LjungrennAudio/ryomodular.com_vert_mx/docs/vertmix/downloads/vertmix pcb 1 schematic.png

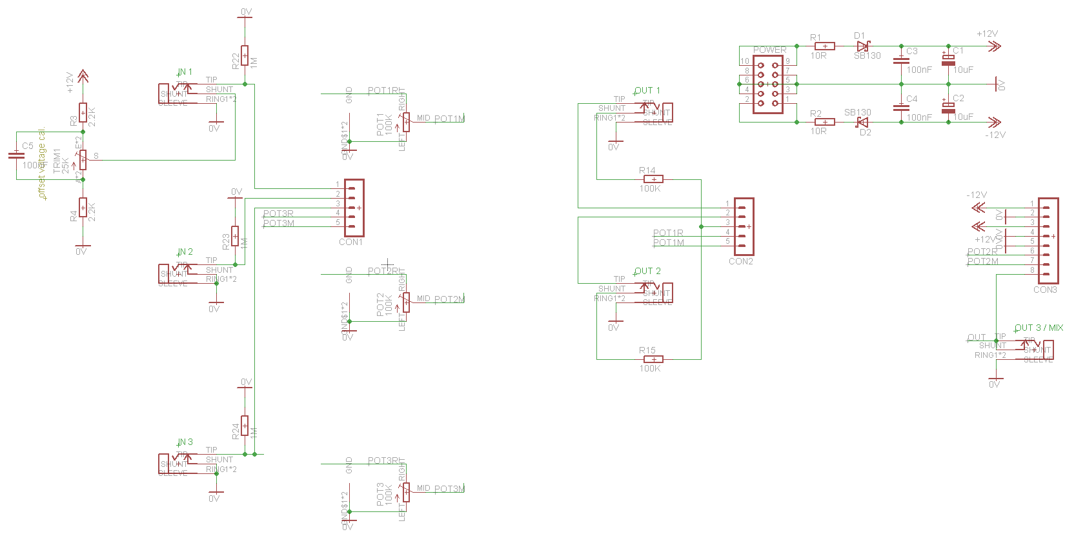
docs/vertmix/downloads/vertmix pcb 1 schematic.png
