LjungrennAudio/ryomodular.com_vert_mx/src/vert_mx - Copy.png

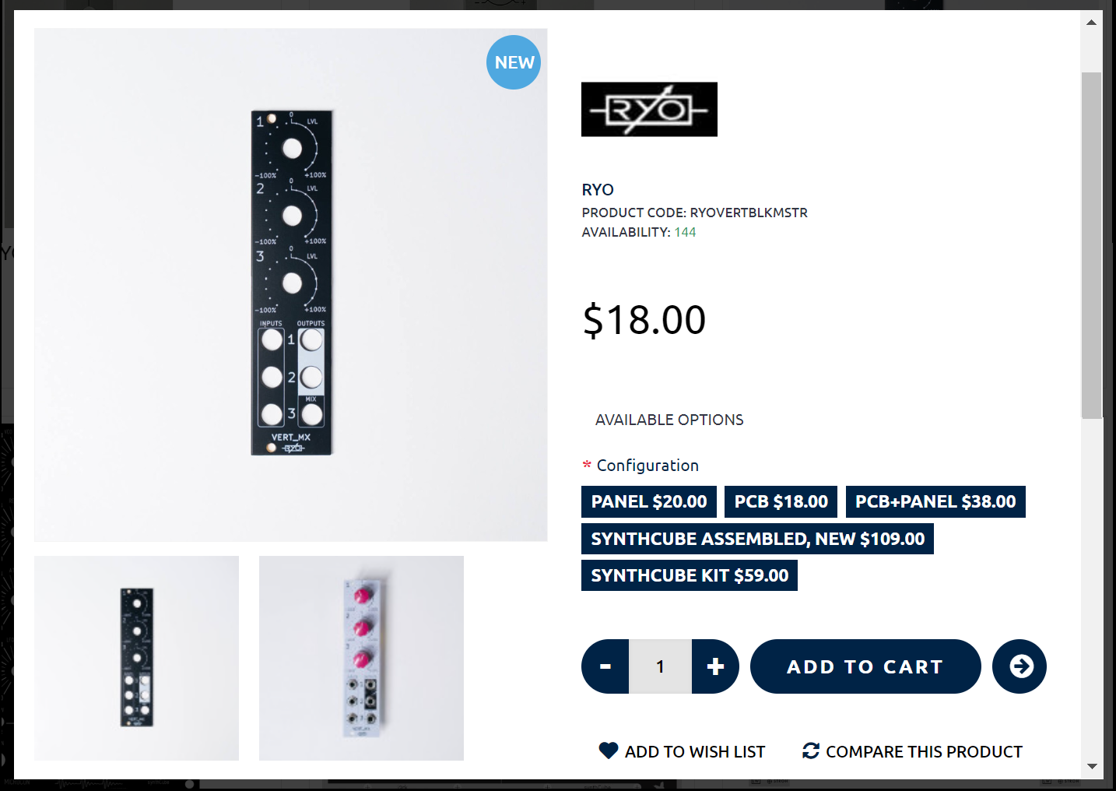
src/vert_mx - Copy.png
