LjungrennAudio/ryomodular.com_vert_mx/src/vert_mx/ryomodular-vert_mx-schem-202411160015.png

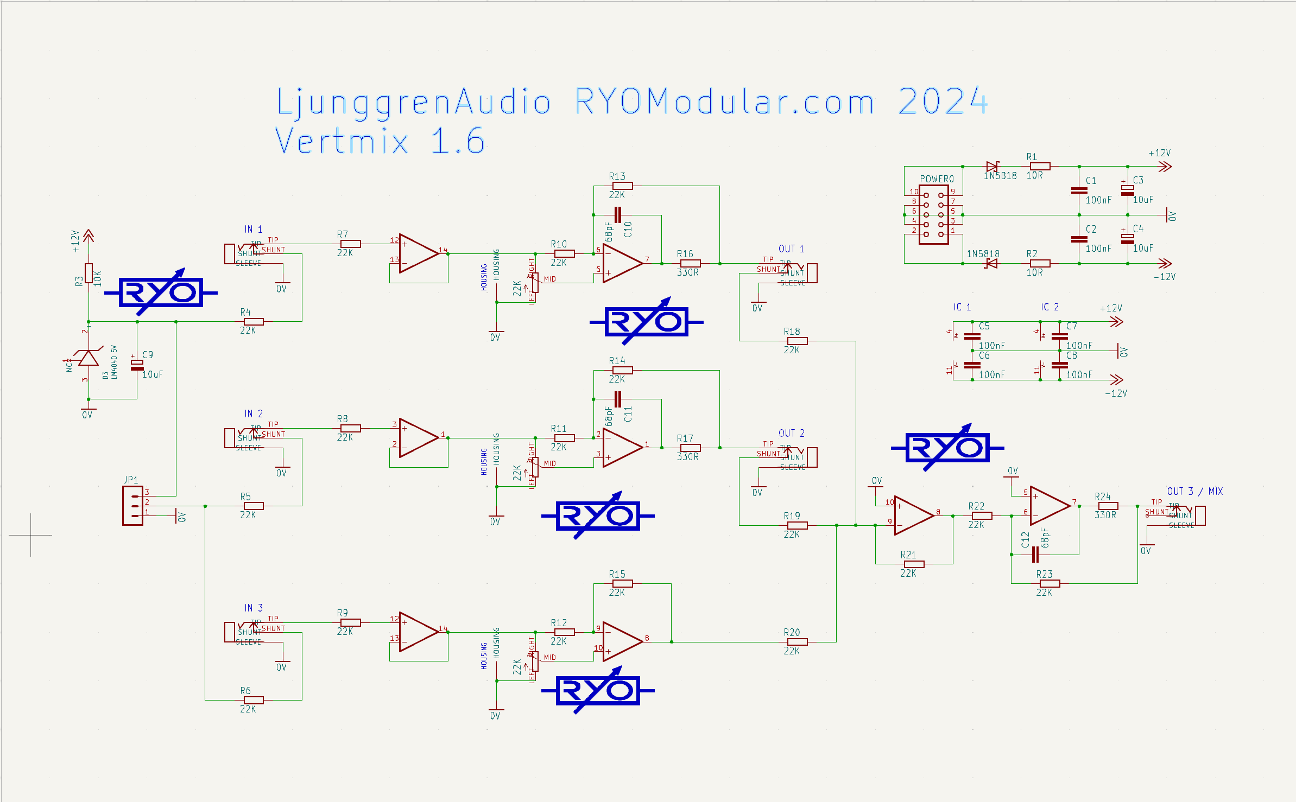
src/vert_mx/ryomodular-vert_mx-schem-202411160015.png
