LjungrennAudio/ryomodular.com_vert_mx/src/vert_mx_schematic_2410021019 - Copy.gif

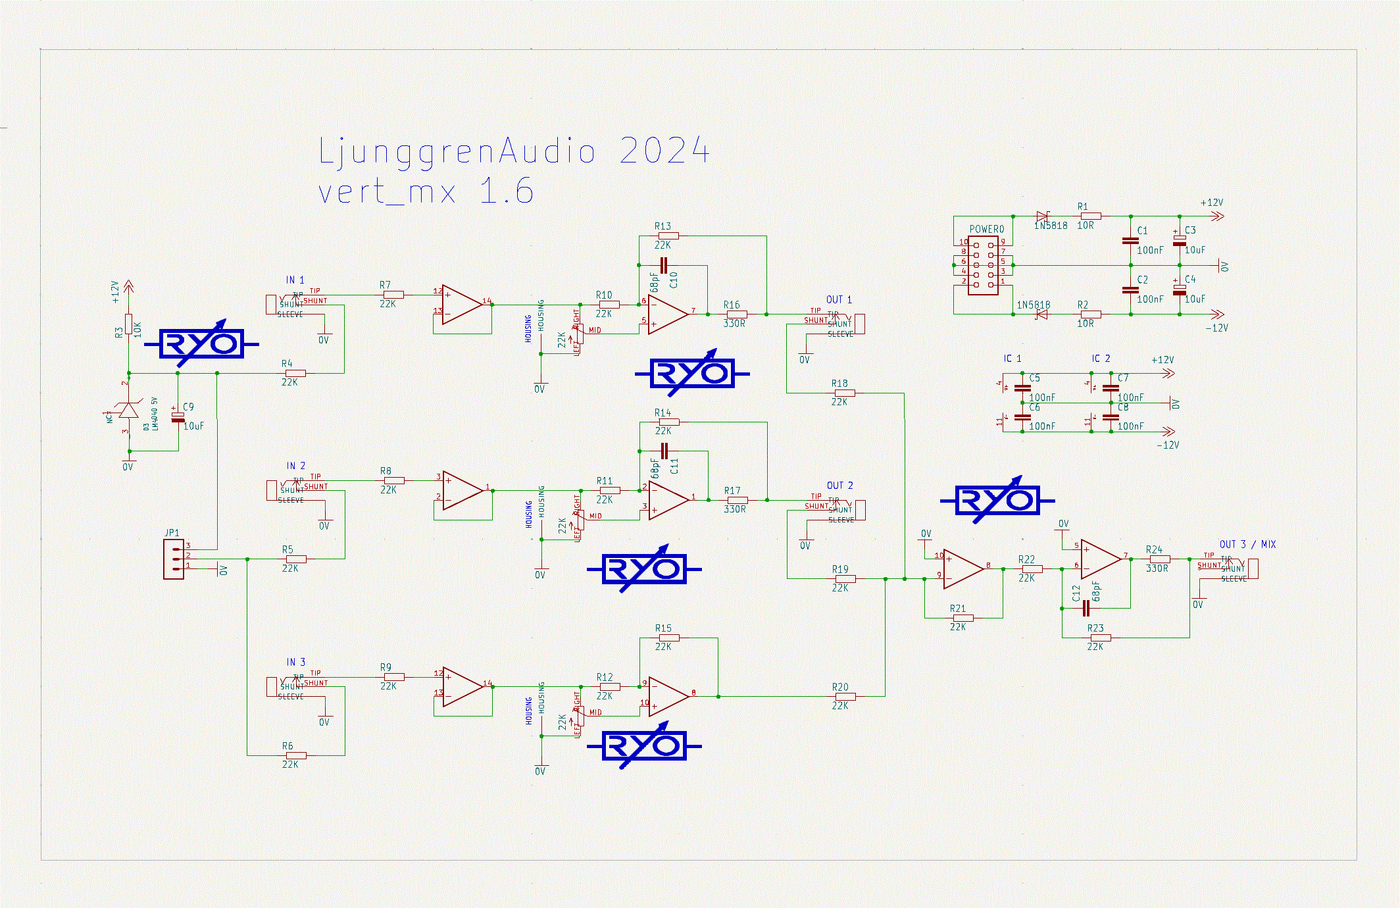
src/vert_mx_schematic_2410021019 - Copy.gif
