LjungrennAudio/ryomodular.com_vert_mx/src/vertmix_docs_etc-/Bipolar mixer-att 1.0.png

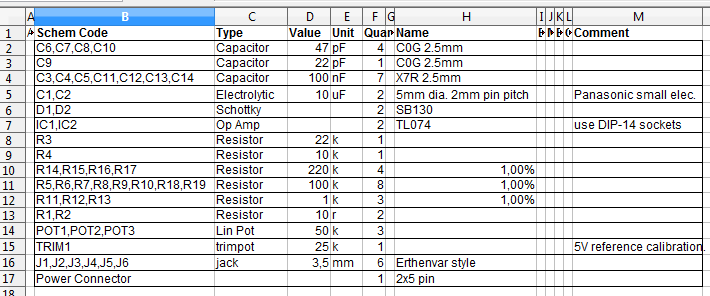
src/vertmix_docs_etc-/Bipolar mixer-att 1.0.png
