LjungrennAudio/ryomodular.com_vert_mx/builds/ryo_vert_mx/3ch mix.brd

## EAGLE design builds/ryo_vert_mx/3ch mix.brd (2024-09-06)

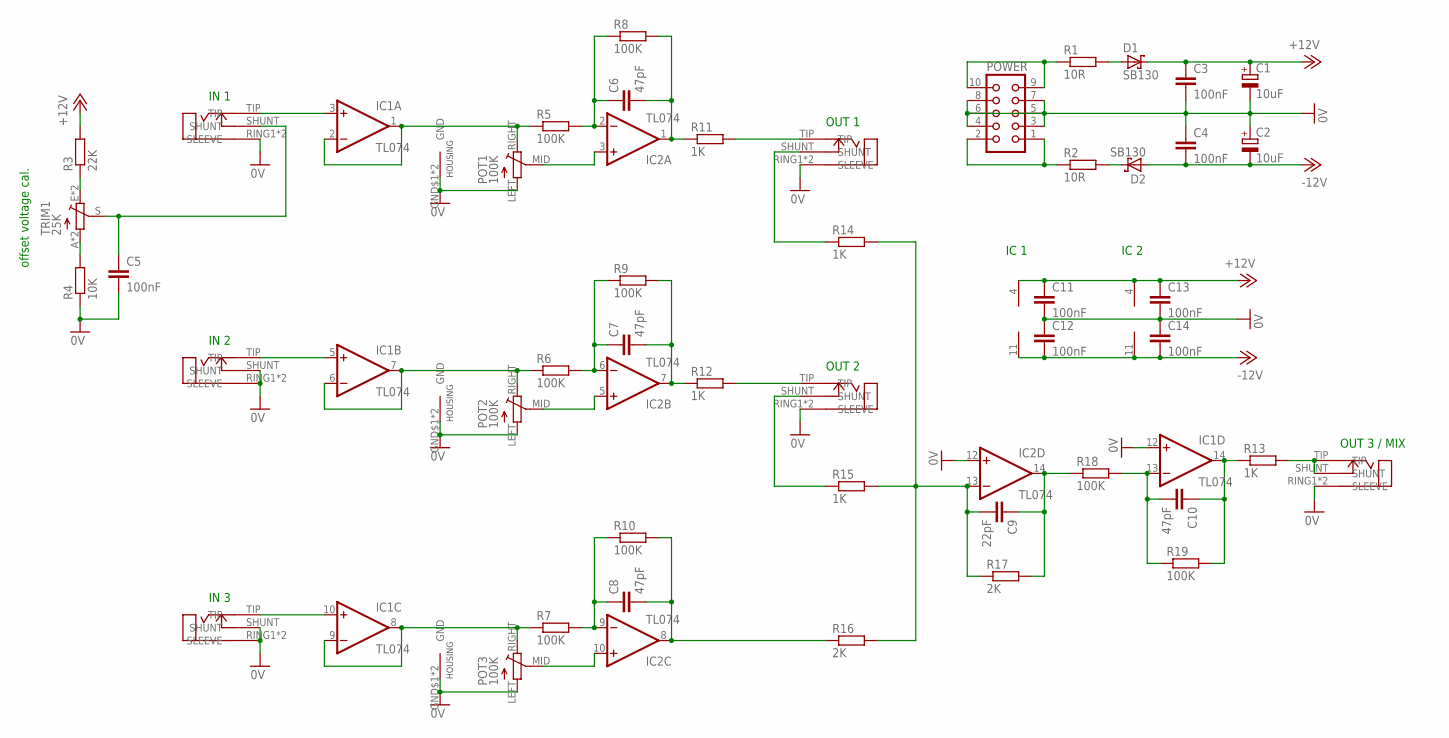
[picture p53: schematic 3ch mix.sch]

Parts:
C1, C2: 10uF; E2-5
C3, C4, C5, C11, C12, C13, C14: 100nF; C025-024X044
C6, C7, C8, C10: 47pF; C025-024X044
C9: 22pF; C025-024X044
D1, D2: SB130; DO41-7
IC1, IC2: TL074; DIL14
IN1, IN2, IN3: ERTHENVAR_3.5MM_JACK; ERTHENVAR
OUT1, OUT2, OUT3: ERTHENVAR_3.5MM_JACK; ERTHENVAR
POT1, POT2, POT3: 100K; POT-ALPHA9
POWER: CON10L
R1, R2: 10R; 0207/9
R3: 22K; 0207/9
R4: 10K; 0207/9
R5, R6, R7, R8, R9, R10, R18, R19: 100K; 0207/9
R11, R12, R13, R14, R15: 1K; 0207/9
R16, R17: 2K; 0207/9
TRIM1: 25K; B25P

Connections:
0V: C1.-, C2.+, C3.2, C4.1, C5.2, C11.2, C12.1, C13.2, C14.1, IC1.12 (+IN), IC2.12 (+IN), IN1.RING1 (SLEEVE), IN1.RING2 (SLEEVE), IN2.RING1 (SLEEVE), IN2.RING2 (SLEEVE), IN2.SHUNT, IN3.RING1 (SLEEVE), IN3.RING2 (SLEEVE), IN3.SHUNT, OUT1.RING1 (SLEEVE), OUT1.RING2 (SLEEVE), OUT2.RING1 (SLEEVE), OUT2.RING2 (SLEEVE), OUT3.RING1 (SLEEVE), OUT3.RING2 (SLEEVE), POT1.GND$1 (GND), POT1.GND$2 (GND), POT1.LEFT, POT2.GND$1 (GND), POT2.GND$2 (GND), POT2.LEFT, POT3.GND$1 (GND), POT3.GND$2 (GND), POT3.LEFT, POWER.3, POWER.4, POWER.5, POWER.6, POWER.7, POWER.8, R4.1
+12V: C1.+, C3.1, C11.1, C13.1, D1.C, IC1.4 (V+), IC2.4 (V+), R3.2
-12V: C2.-, C4.2, C12.2, C14.2, D2.A, IC1.11 (V-), IC2.11 (V-)
unnamed: POWER.9, POWER.10, R1.1
unnamed: POWER.1, POWER.2, R2.1
unnamed: R4.2, TRIM1.A, TRIM1.AA (A)
unnamed: D1.A, R1.2
unnamed: D2.C, R2.2
unnamed: R3.1, TRIM1.E, TRIM1.EE (E)
unnamed: C5.1, IN1.SHUNT, TRIM1.S
unnamed: IC1.3 (+IN), IN1.TIP
unnamed: IC1.5 (+IN), IN2.TIP
unnamed: IC1.10 (+IN), IN3.TIP
unnamed: IC1.1 (OUT), IC1.2 (-IN), POT1.RIGHT, R5.1
unnamed: IC1.6 (-IN), IC1.7 (OUT), POT2.RIGHT, R6.1
unnamed: IC1.8 (OUT), IC1.9 (-IN), POT3.RIGHT, R7.1
unnamed: C6.1, IC2.2 (-IN), R5.2, R8.1
unnamed: IC2.3 (+IN), POT1.MID
unnamed: IC2.5 (+IN), POT2.MID
unnamed: IC2.10 (+IN), POT3.MID
unnamed: OUT1.TIP, R11.2
unnamed: OUT2.TIP, R12.2
unnamed: C7.1, IC2.6 (-IN), R6.2, R9.1
unnamed: C8.1, IC2.9 (-IN), R7.2, R10.1
unnamed: C6.2, IC2.1 (OUT), R8.2, R11.1
unnamed: C7.2, IC2.7 (OUT), R9.2, R12.1
unnamed: C8.2, IC2.8 (OUT), R10.2, R16.1
unnamed: OUT1.SHUNT, R14.1
unnamed: OUT2.SHUNT, R15.1
unnamed: C9.2, IC2.13 (-IN), R14.2, R15.2, R16.2, R17.1
unnamed: C9.1, IC2.14 (OUT), R17.2, R18.1
unnamed: C10.2, IC1.13 (-IN), R18.2, R19.1
unnamed: C10.1, IC1.14 (OUT), R13.1, R19.2
unnamed: OUT3.SHUNT, OUT3.TIP, R13.2

Notes on the sheet:
offset voltage cal.
IN 1
IN 2
IN 3
OUT 1
OUT 2
OUT 3 / MIX
IC 1
IC 2
HOUSING

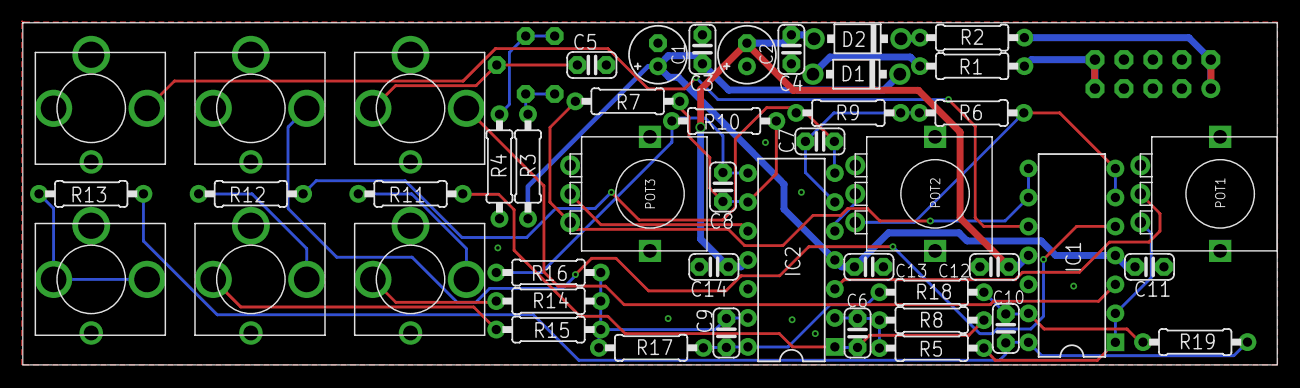
[picture p54: board 3ch mix.brd from above]

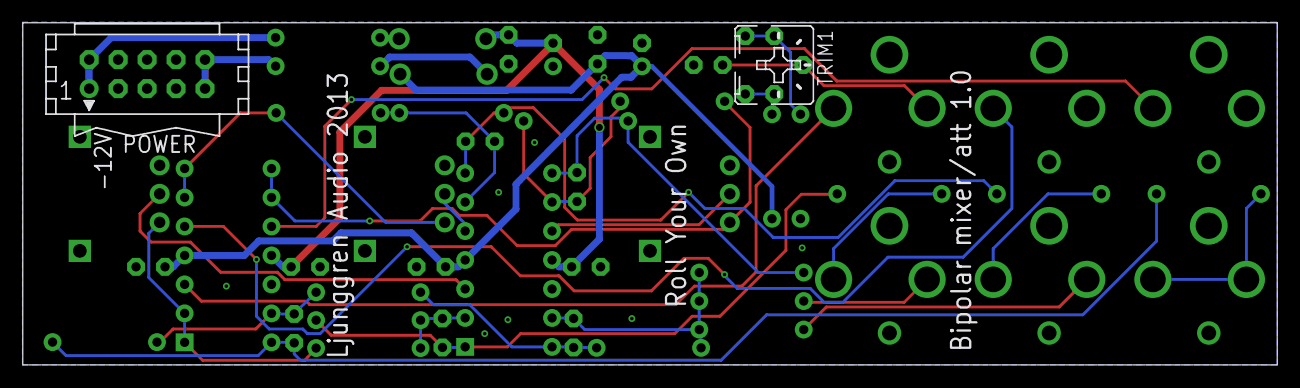
[picture p55: board 3ch mix.brd from below]

Board: 2 copper layers, 110.0 x 30.0 mm, 48 parts (2 on the bottom side), 34 nets.
