LjungrennAudio/ryomodular.com_vert_mx/builds/ryo_vert_mx/PCB1 1.1.brd

## EAGLE design builds/ryo_vert_mx/PCB1 1.1.brd (2024-09-06)

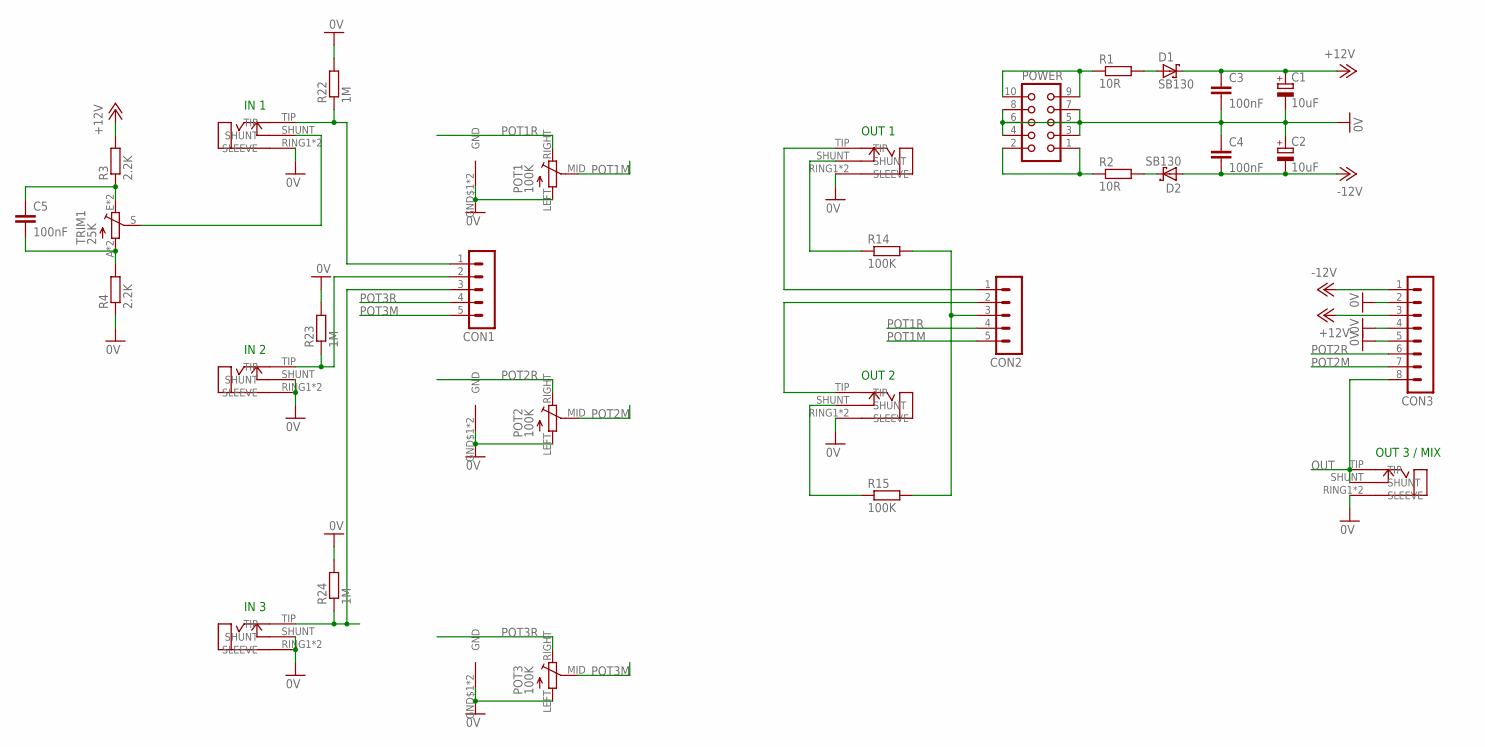
[picture p56: schematic PCB1 1.1.sch]

Parts:
C1, C2: 10uF; E2-5
C3, C4, C5: 100nF; C025-024X044
CON1, CON2: MA05-1
CON3: MA08-1
D1, D2: SB130; DO41-7
IN1, IN2, IN3: ERTHENVAR_3.5MM_JACK; ERTHENVAR
OUT1, OUT2, OUT3: ERTHENVAR_3.5MM_JACK; ERTHENVAR
POT1, POT2, POT3: 100K; POT-ALPHA9
POWER: CON10L
R1, R2: 10R; 0207/9
R3, R4: 2.2K; 0207/9
R14, R15: 100K; 0207/9
R22, R23, R24: 1M; 0207/9
TRIM1: 25K; B25P

Connections:
0V: C1.-, C2.+, C3.2, C4.1, CON3.2, CON3.4, CON3.5, IN1.RING1 (SLEEVE), IN1.RING2 (SLEEVE), IN2.RING1 (SLEEVE), IN2.RING2 (SLEEVE), IN2.SHUNT, IN3.RING1 (SLEEVE), IN3.RING2 (SLEEVE), IN3.SHUNT, OUT1.RING1 (SLEEVE), OUT1.RING2 (SLEEVE), OUT2.RING1 (SLEEVE), OUT2.RING2 (SLEEVE), OUT3.RING1 (SLEEVE), OUT3.RING2 (SLEEVE), POT1.GND$1 (GND), POT1.GND$2 (GND), POT1.LEFT, POT2.GND$1 (GND), POT2.GND$2 (GND), POT2.LEFT, POT3.GND$1 (GND), POT3.GND$2 (GND), POT3.LEFT, POWER.3, POWER.4, POWER.5, POWER.6, POWER.7, POWER.8, R4.1, R22.2, R23.2, R24.2
+12V: C1.+, C3.1, CON3.3, D1.C, R3.2
-12V: C2.-, C4.2, CON3.1, D2.A
unnamed: POWER.9, POWER.10, R1.1
unnamed: POWER.1, POWER.2, R2.1
unnamed: C5.2, R4.2, TRIM1.A, TRIM1.AA (A)
unnamed: D1.A, R1.2
unnamed: D2.C, R2.2
unnamed: C5.1, R3.1, TRIM1.E, TRIM1.EE (E)
unnamed: IN1.SHUNT, TRIM1.S
unnamed: CON1.1, IN1.TIP, R22.1
unnamed: CON1.2, IN2.TIP, R23.1
unnamed: CON1.3, IN3.TIP, R24.1
unnamed: CON2.1, OUT1.TIP
unnamed: CON2.2, OUT2.TIP
unnamed: OUT1.SHUNT, R14.1
unnamed: OUT2.SHUNT, R15.1
unnamed: CON2.3, R14.2, R15.2
OUT: CON3.8, OUT3.SHUNT, OUT3.TIP
POT1M: CON2.5, POT1.MID
POT1R: CON2.4, POT1.RIGHT
POT2M: CON3.7, POT2.MID
POT2R: CON3.6, POT2.RIGHT
POT3M: CON1.5, POT3.MID
POT3R: CON1.4, POT3.RIGHT

Notes on the sheet:
IN 1
IN 2
IN 3
OUT 1
OUT 2
OUT 3 / MIX

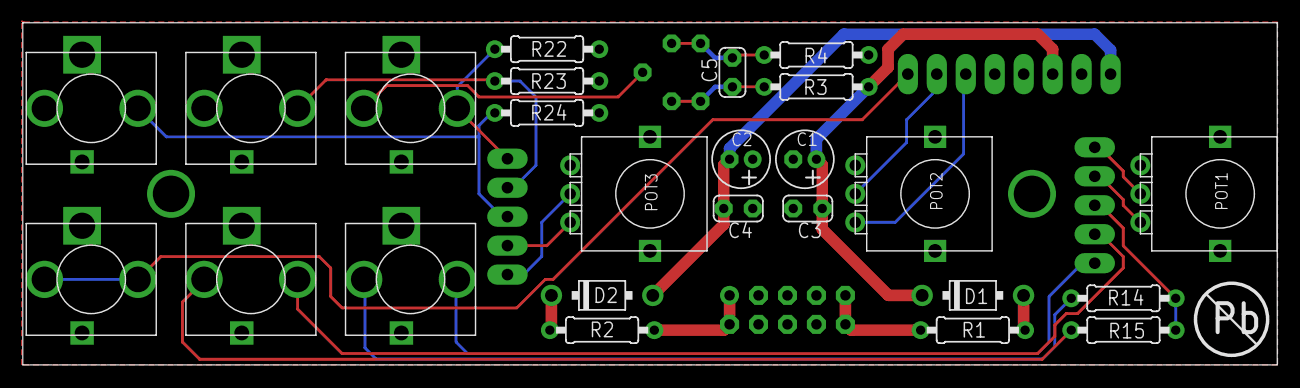
[picture p57: board PCB1 1.1.brd from above]

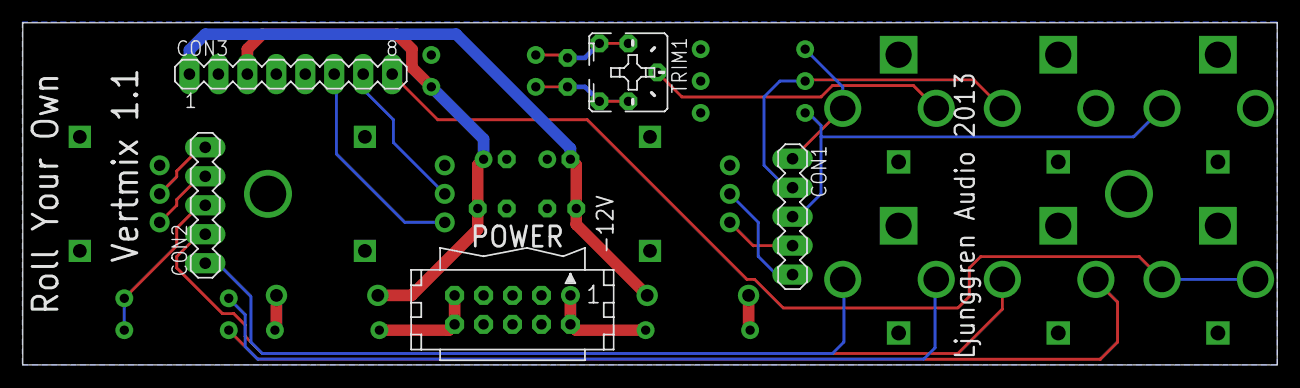
[picture p58: board PCB1 1.1.brd from below]

Board: 2 copper layers, 110.0 x 30.0 mm, 30 parts (5 on the bottom side), 25 nets.
