LjungrennAudio/ryomodular.com_vert_mx/builds/ryo_vert_mx/PCB2 1.1.brd

## EAGLE design builds/ryo_vert_mx/PCB2 1.1.brd (2024-09-06)

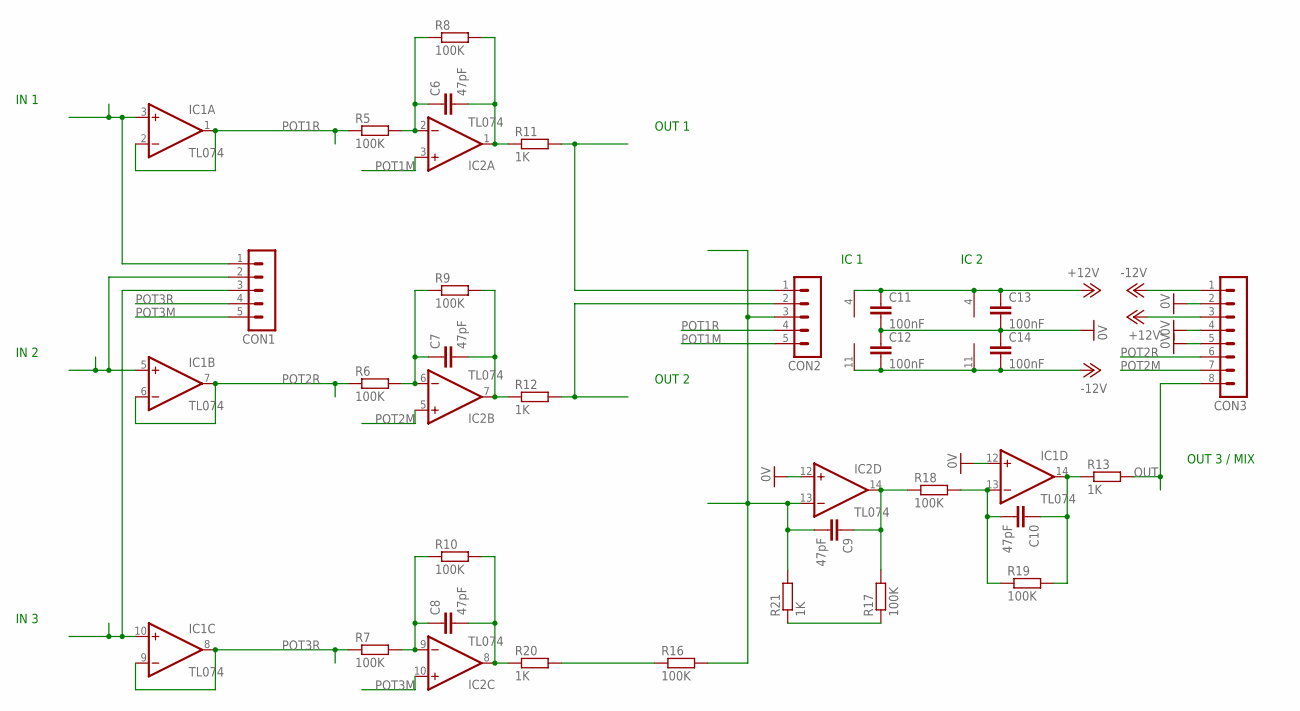
[picture p59: schematic PCB2 1.1.sch]

Parts:
C6, C7, C8, C9, C10: 47pF; C025-024X044
C11, C12, C13, C14: 100nF; C025-024X044
CON1, CON2: MA05-1
CON3: MA08-1
IC1, IC2: TL074; DIL14
R5, R6, R7, R8, R9, R10, R16, R17, R18, R19: 100K; 0207/9
R11, R12, R13, R20, R21: 1K; 0207/9

Connections:
0V: C11.2, C12.1, C13.2, C14.1, CON3.2, CON3.4, CON3.5, IC1.12 (+IN), IC2.12 (+IN)
+12V: C11.1, C13.1, CON3.3, IC1.4 (V+), IC2.4 (V+)
-12V: C12.2, C14.2, CON3.1, IC1.11 (V-), IC2.11 (V-)
unnamed: R16.1, R20.2
unnamed: CON1.1, IC1.3 (+IN)
unnamed: CON1.2, IC1.5 (+IN)
unnamed: CON1.3, IC1.10 (+IN)
unnamed: C6.1, IC2.2 (-IN), R5.2, R8.1
unnamed: CON2.1, R11.2
unnamed: CON2.2, R12.2
unnamed: C7.1, IC2.6 (-IN), R6.2, R9.1
unnamed: C8.1, IC2.9 (-IN), R7.2, R10.1
unnamed: C6.2, IC2.1 (OUT), R8.2, R11.1
unnamed: C7.2, IC2.7 (OUT), R9.2, R12.1
unnamed: C8.2, IC2.8 (OUT), R10.2, R20.1
unnamed: R17.1, R21.1
unnamed: C9.1, IC2.14 (OUT), R17.2, R18.1
unnamed: C10.2, IC1.13 (-IN), R18.2, R19.1
unnamed: C10.1, IC1.14 (OUT), R13.1, R19.2
unnamed: C9.2, CON2.3, IC2.13 (-IN), R16.2, R21.2
OUT: CON3.8, R13.2
POT1M: CON2.5, IC2.3 (+IN)
POT1R: CON2.4, IC1.1 (OUT), IC1.2 (-IN), R5.1
POT2M: CON3.7, IC2.5 (+IN)
POT2R: CON3.6, IC1.6 (-IN), IC1.7 (OUT), R6.1
POT3M: CON1.5, IC2.10 (+IN)
POT3R: CON1.4, IC1.8 (OUT), IC1.9 (-IN), R7.1

Notes on the sheet:
IN 1
IN 2
IN 3
OUT 1
OUT 2
OUT 3 / MIX
IC 1
IC 2

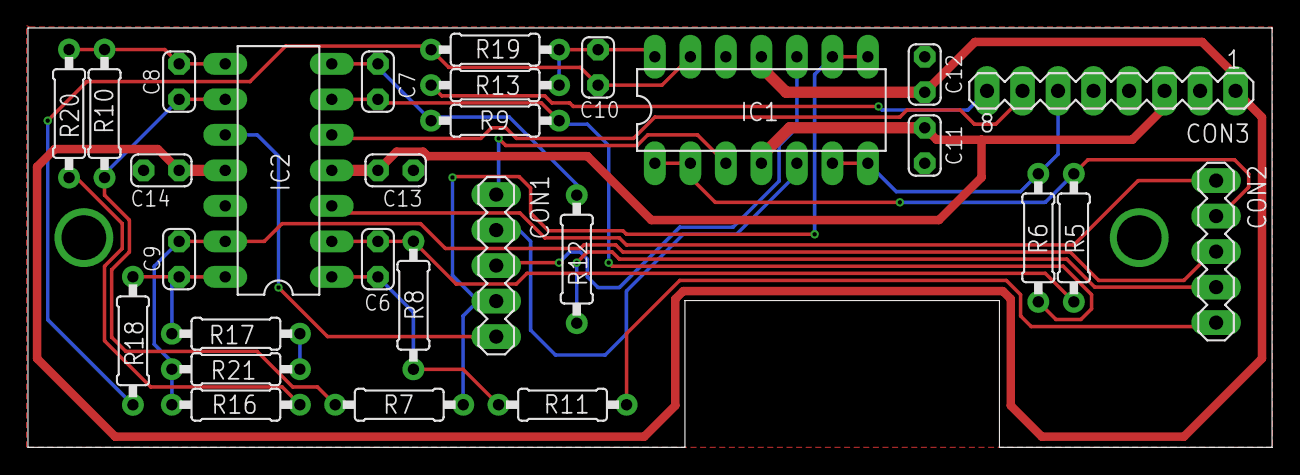
[picture p60: board PCB2 1.1.brd from above]

Board: 2 copper layers, 89.0 x 30.0 mm, 29 parts (0 on the bottom side), 27 nets.
